SaturnR/TurtlePi/pi_python_arduino_files/image.jpg

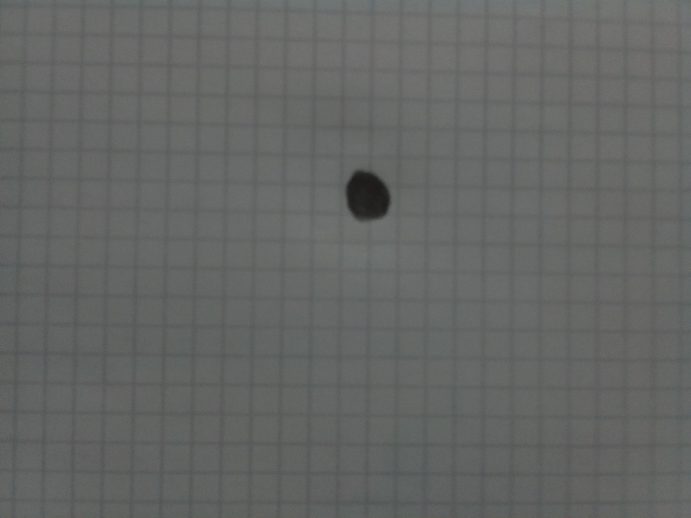
pi_python_arduino_files/image.jpg
