SaturnR/TurtlePi/rob_pic/2014-04-22 18.00.07.jpg

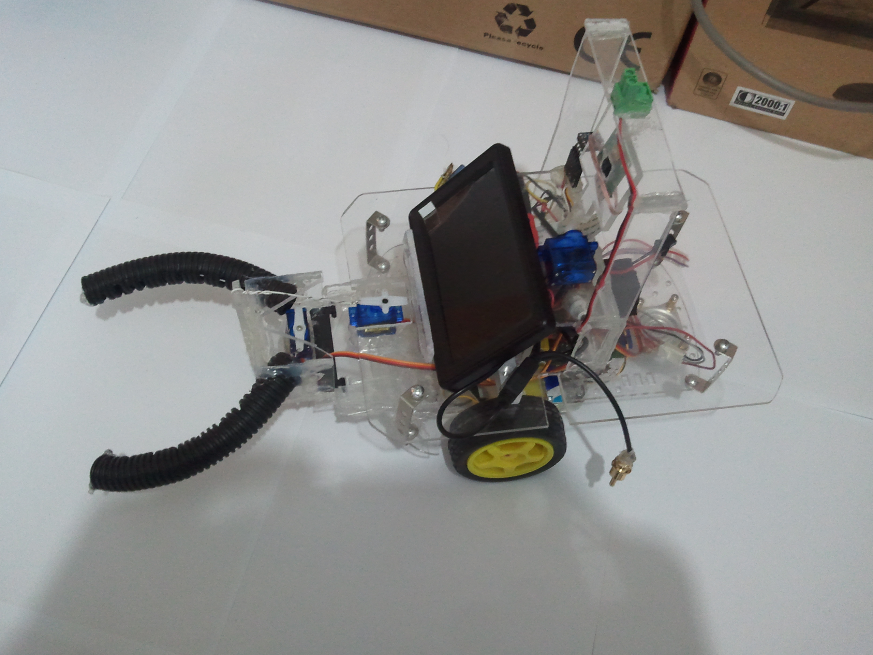
rob_pic/2014-04-22 18.00.07.jpg
