SaturnR/TurtlePi/rob_pic/2014-04-22 19.34.48.jpg

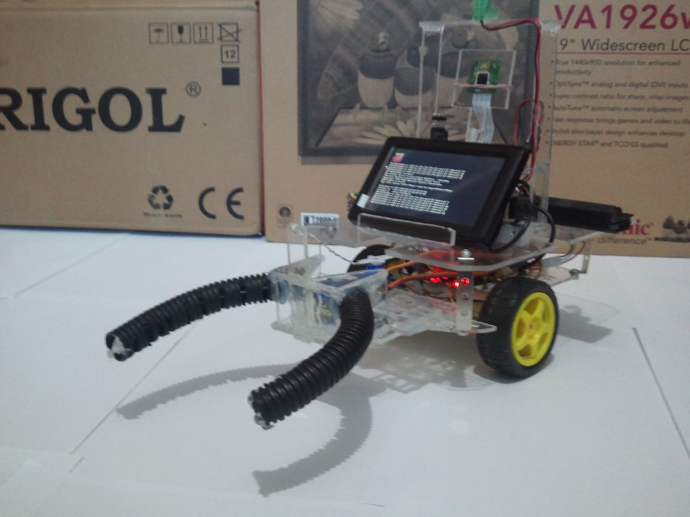
rob_pic/2014-04-22 19.34.48.jpg
