SaturnR/TurtlePi/rob_pic/2014-04-22 19.35.43.jpg

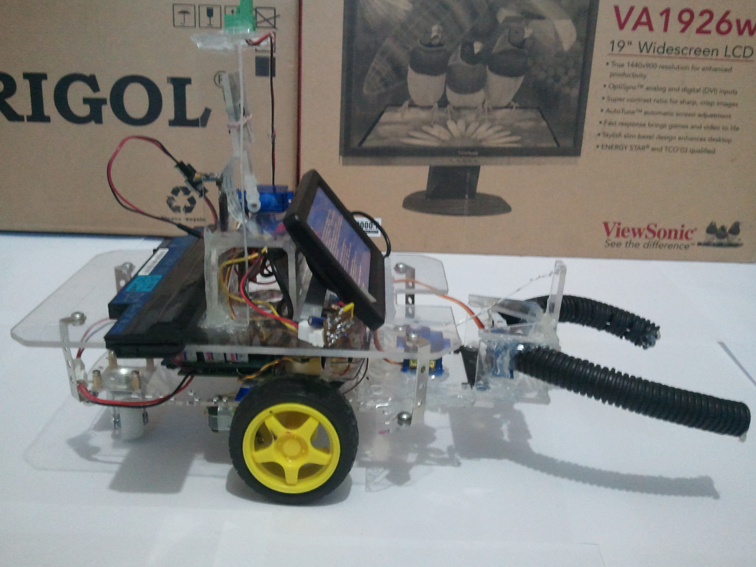
rob_pic/2014-04-22 19.35.43.jpg
