SaturnR/TurtlePi/rob_pic/2014-04-22 19.36.45.jpg

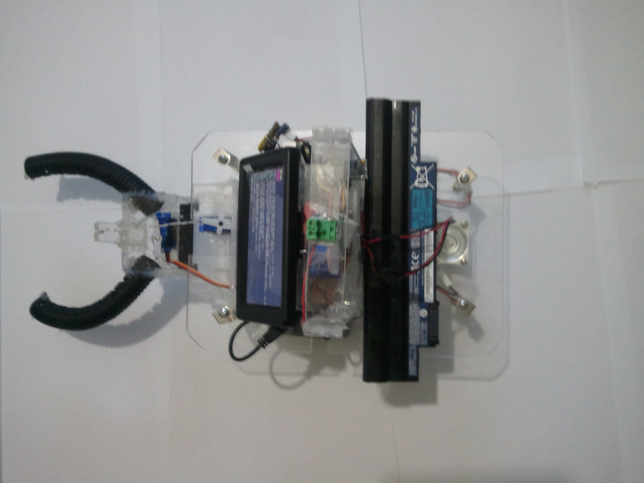
rob_pic/2014-04-22 19.36.45.jpg
