SaturnR/TurtlePi/rob_pic/2014-04-22 19.43.05.jpg

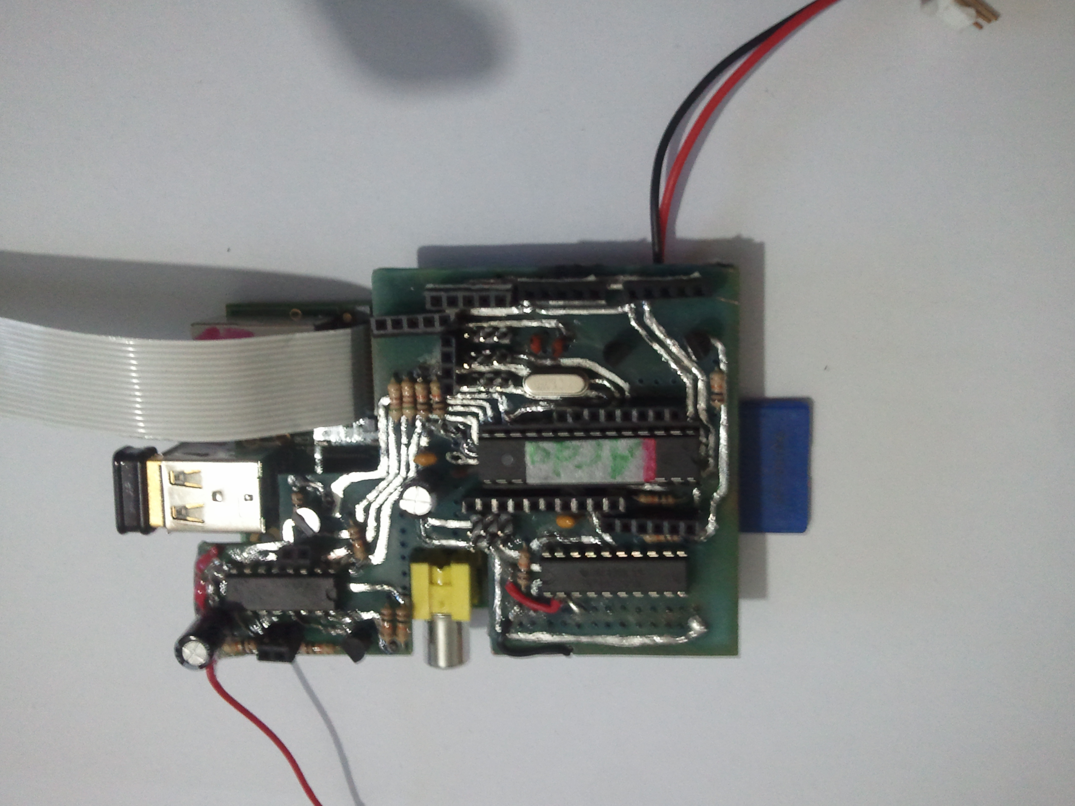
rob_pic/2014-04-22 19.43.05.jpg
