SaturnR/TurtlePi/rob_pic/2014-04-22 19.44.24.jpg

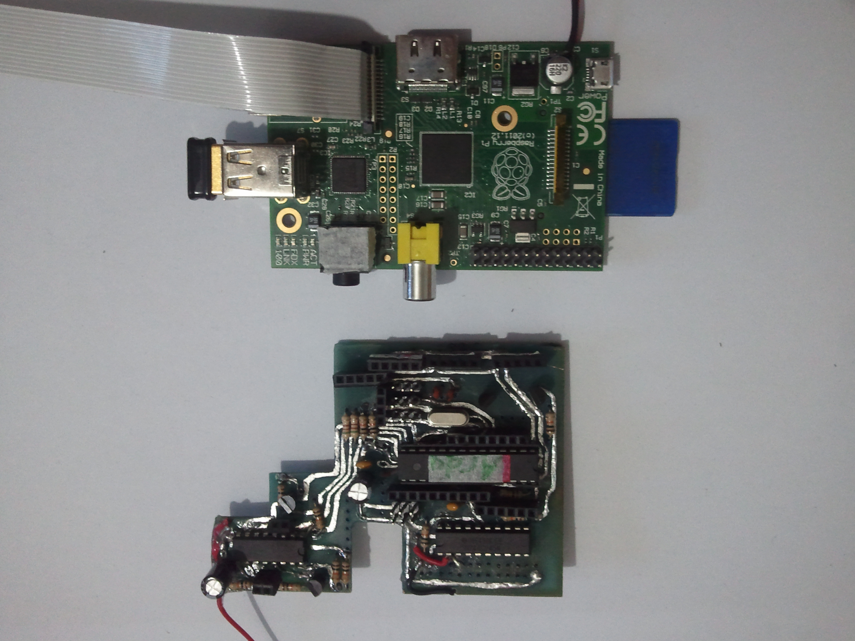
rob_pic/2014-04-22 19.44.24.jpg
