SaturnR/TurtlePi/Robot_cad/Renderings/Raspberry.jpg

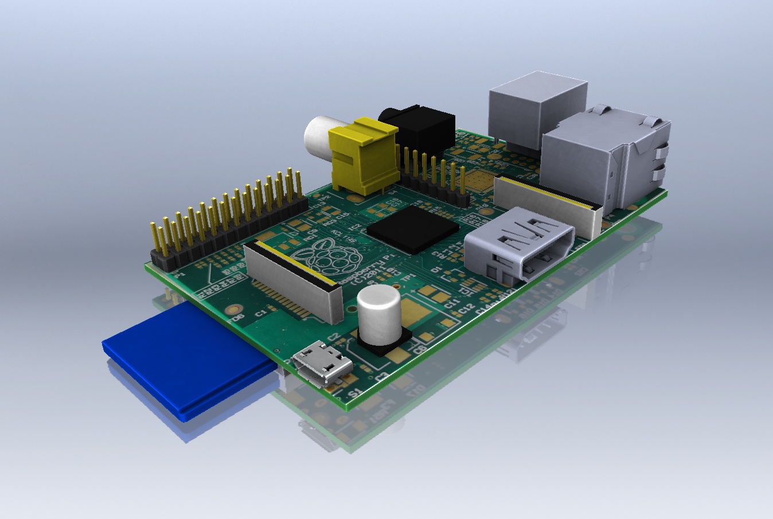
Robot_cad/Renderings/Raspberry.jpg
