SaturnR/TurtlePi/Robot_cad/Renderings/raspberry.png

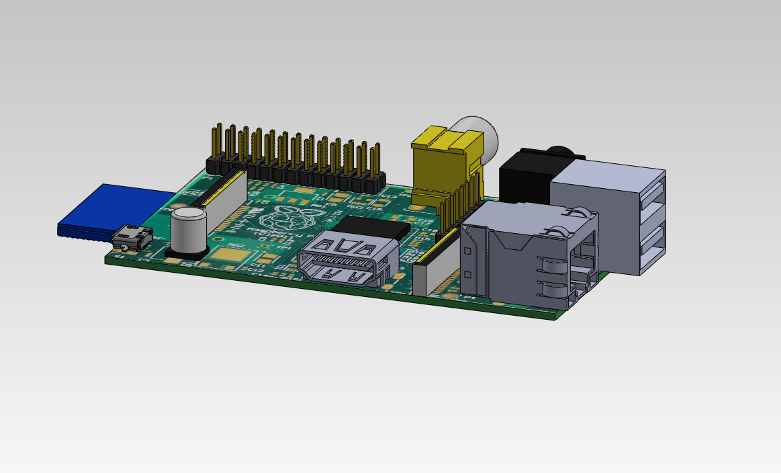
Robot_cad/Renderings/raspberry.png
