SaturnR/TurtlePi/Robot_cad/Renderings/RPi with enclosure.JPG

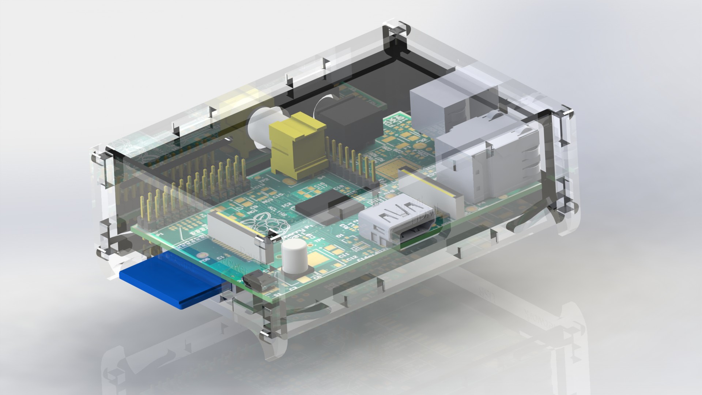
Robot_cad/Renderings/RPi with enclosure.JPG
