SaturnR/TurtlePi/Robot_cad/robot.fcstd

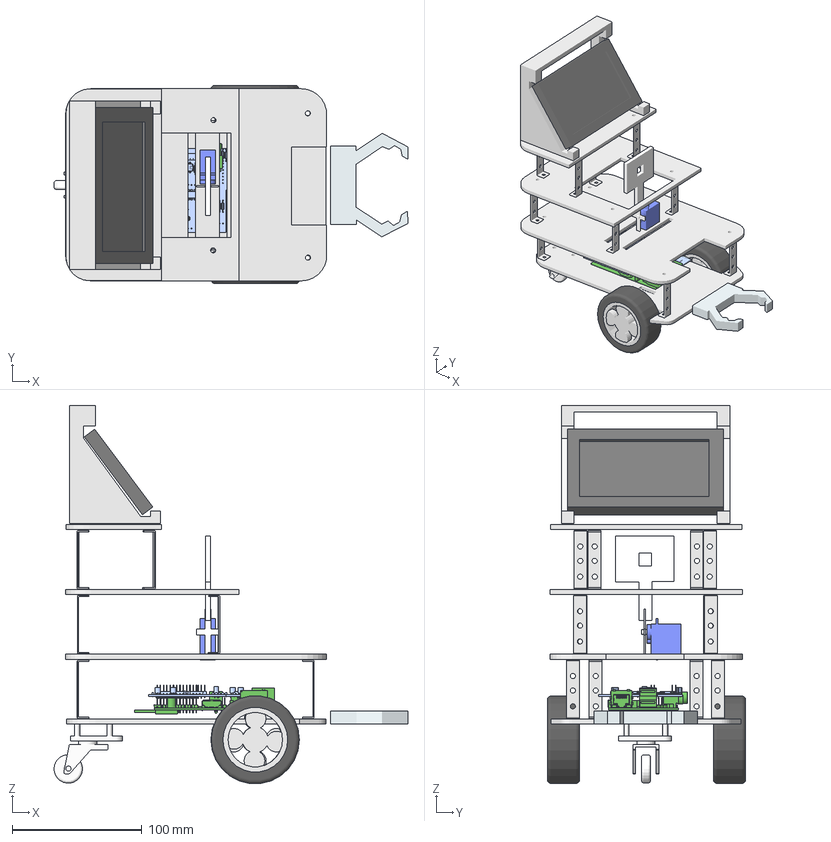
[picture p27: CAD file, 2014-09-22]
Robot_cad/robot.fcstd
273.1 x 153.0 x 291.6 mm
back_wheel
gripper
display
camera_Pad
RaspBerry
RaspBerry002
RaspBerry004
RaspBerry006
RaspBerry008
RaspBerry010
RaspBerry012
RaspBerry014
RaspBerry016
RaspBerry018
RaspBerry020
RaspBerry022
RaspBerry024
RaspBerry026
RaspBerry028
RaspBerry030
RaspBerry032
RaspBerry034
RaspBerry036
RaspBerry038
RaspBerry040
RaspBerry042
RaspBerry044
RaspBerry046
RaspBerry048
RaspBerry050
RaspBerry052
RaspBerry005
RaspBerry009
RaspBerry013
RaspBerry017
RaspBerry021
RaspBerry025
RaspBerry029
RaspBerry033
RaspBerry037
RaspBerry041
RaspBerry045
RaspBerry049
RaspBerry003
RaspBerry011
RaspBerry019
RaspBerry027
RaspBerry035
RaspBerry043
RaspBerry051
RaspBerry007
RaspBerry023
RaspBerry039
RaspBerry015
RaspBerry047
RaspBerry031
RaspBerry001
rpi_arduino_robot
