SaturnR/TurtlePi/Robot_cad/Arm11.SLDPRT

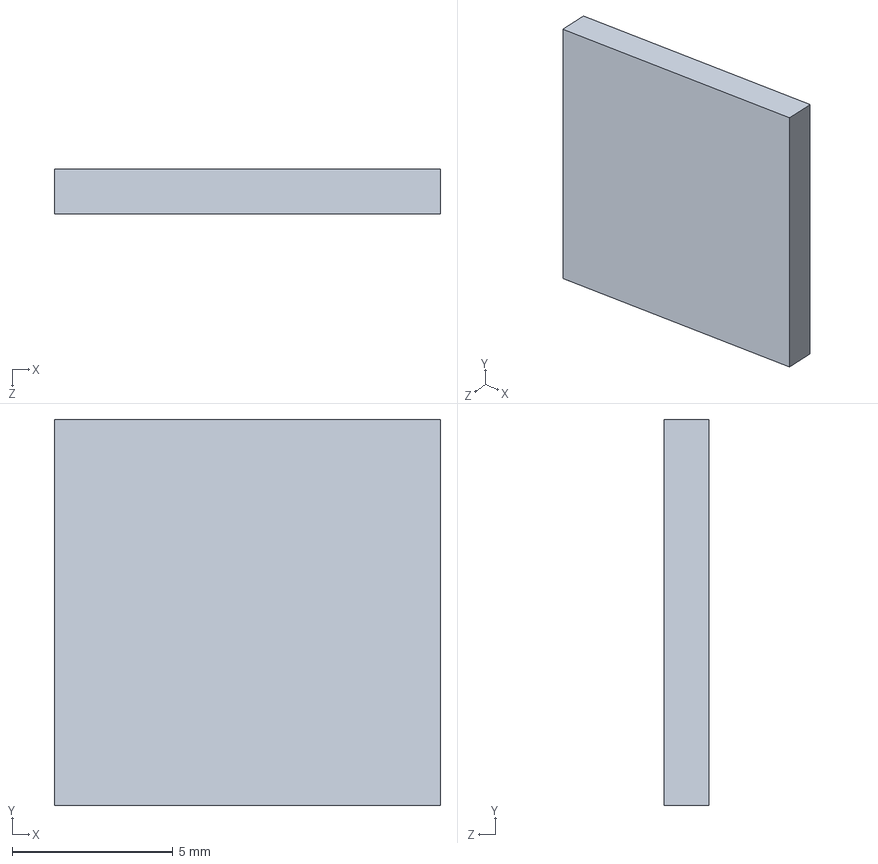
[picture p28: CAD file, 2014-09-22]
Robot_cad/Arm11.SLDPRT
12.0 x 12.0 x 1.40 mm
