SaturnR/TurtlePi/Robot_cad_01/RJ45.ipt.SLDPRT

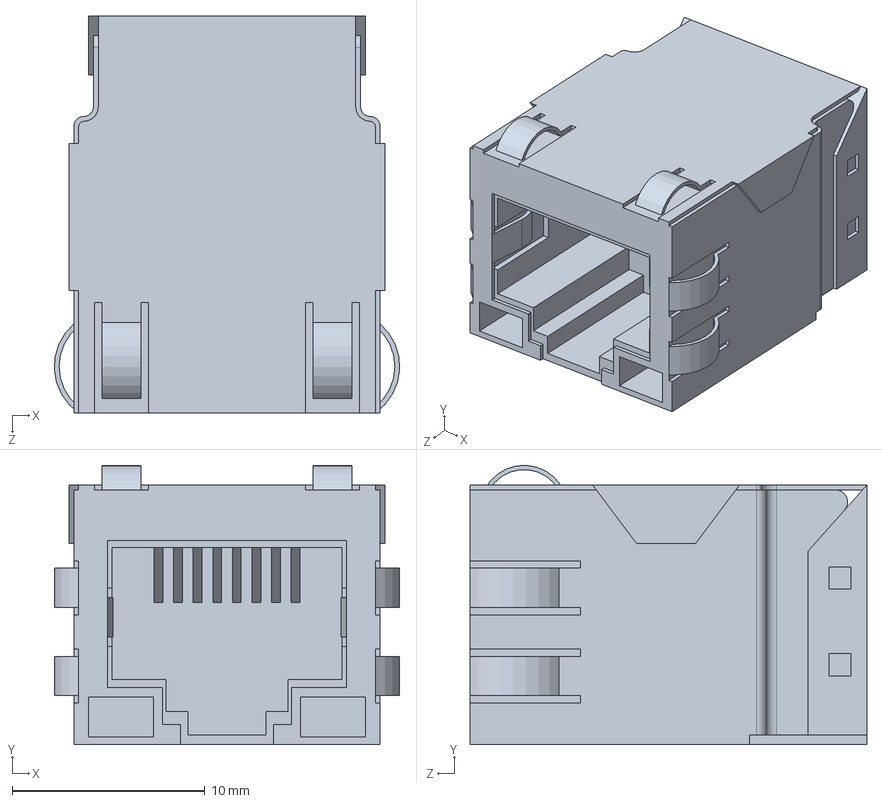
[picture p29: CAD file, 2014-09-22]
Robot_cad_01/RJ45.ipt.SLDPRT
17.9 x 14.5 x 20.6 mm
