SaturnR/TurtlePi/Robot_cad_01/PCB.SLDPRT

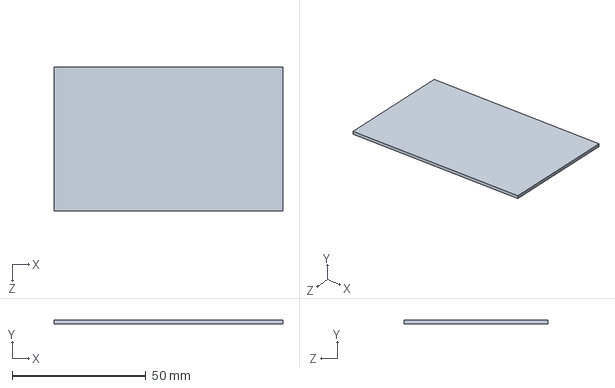
[picture p30: CAD file, 2014-09-22]
Robot_cad_01/PCB.SLDPRT
85.6 x 1.35 x 54.0 mm
