SaturnR/TurtlePi/Robot_cad/HDR2x2.SLDPRT

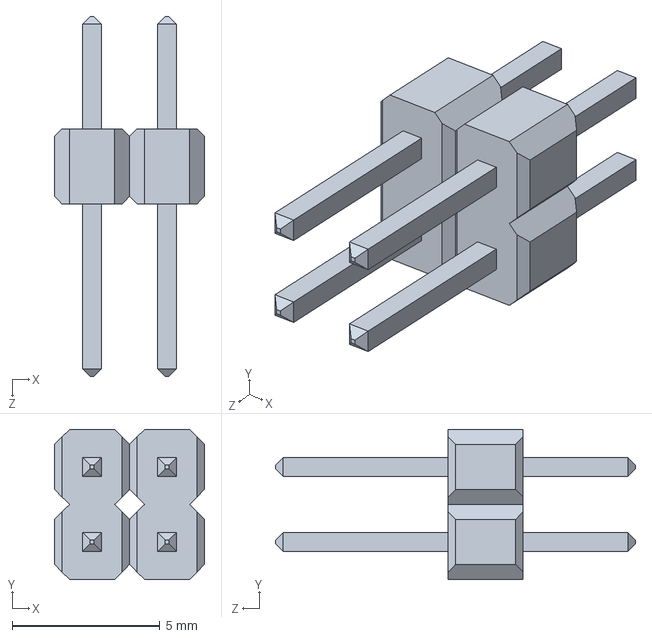
[picture p31: CAD file, 2014-09-22]
Robot_cad/HDR2x2.SLDPRT
5.08 x 5.08 x 12.2 mm
