SaturnR/TurtlePi/Robot_cad_01/micro usb02.SLDPRT

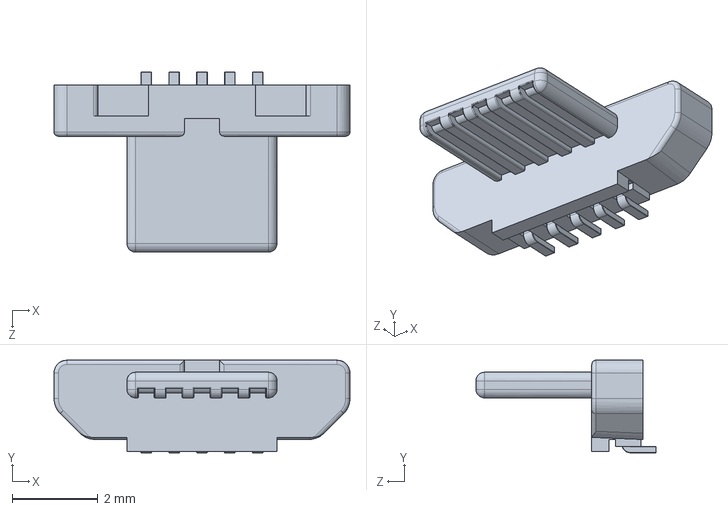
[picture p32: CAD file, 2014-09-22]
Robot_cad_01/micro usb02.SLDPRT
6.90 x 2.16 x 4.20 mm
