SaturnR/TurtlePi/Robot_cad_01/User Library-KUSBLX-AS2N-B Dual USB.SLDPRT

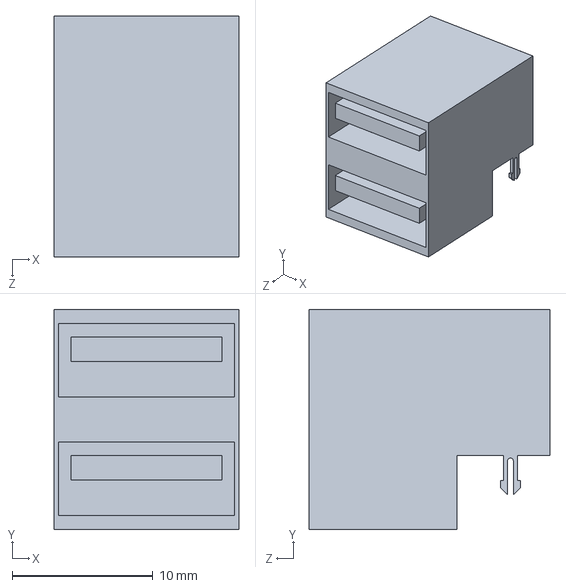
[picture p33: CAD file, 2014-09-22]
Robot_cad_01/User Library-KUSBLX-AS2N-B Dual USB.SLDPRT
13.1 x 15.6 x 17.1 mm
