SaturnR/TurtlePi/Robot_cad/User Library-PJS_05_LB_H.SLDPRT

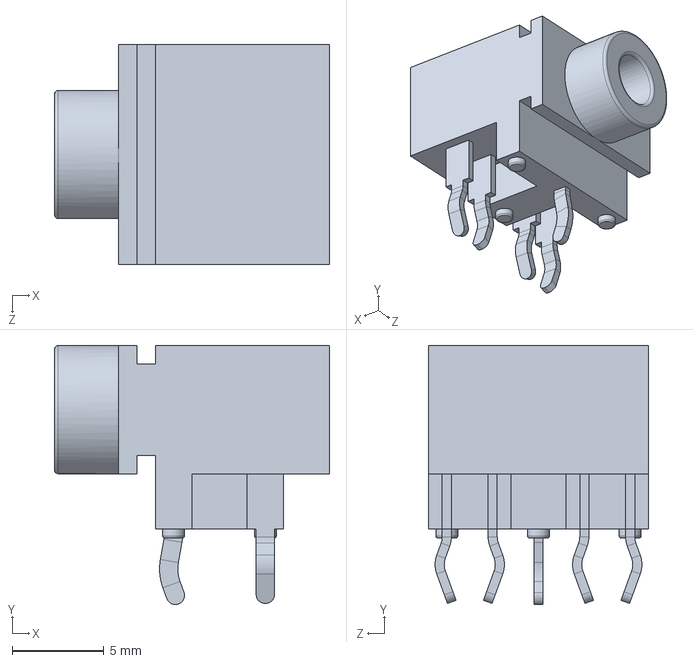
[picture p34: CAD file, 2014-09-22]
Robot_cad/User Library-PJS_05_LB_H.SLDPRT
15.0 x 14.1 x 12.0 mm
