SaturnR/TurtlePi/Robot_cad/HDMI.ipt.SLDPRT

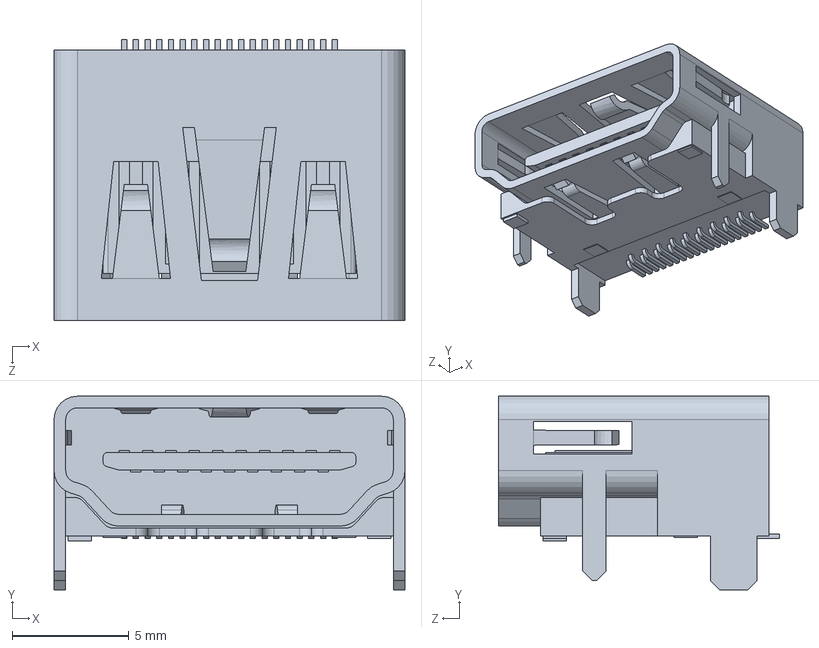
[picture p35: CAD file, 2014-09-22]
Robot_cad/HDMI.ipt.SLDPRT
15.0 x 8.27 x 12.0 mm
